AaronChuzb/TD3/hardwave/SD卡内容（将里边的文件复制到SD卡根目录下）/jpg/2.jpg

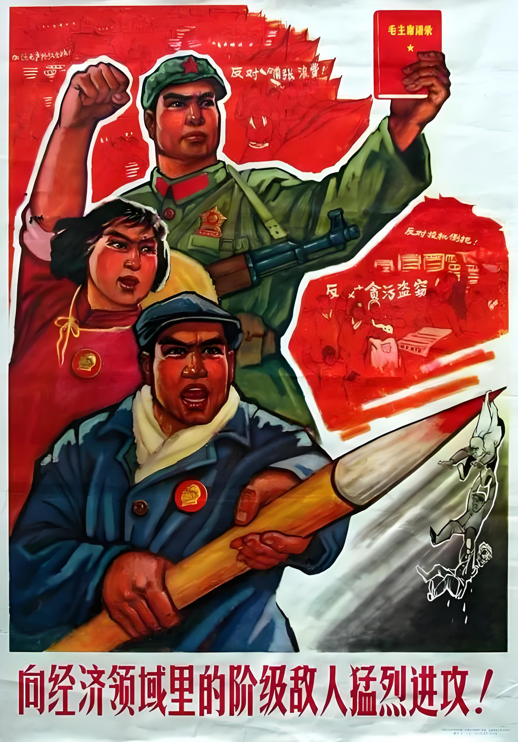
hardwave/SD卡内容（将里边的文件复制到SD卡根目录下）/jpg/2.jpg
