AaronChuzb/TD3/hardwave/SD卡内容（将里边的文件复制到SD卡根目录下）/png/1.png

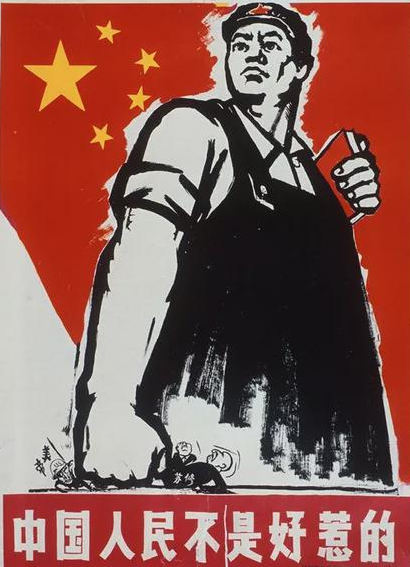
hardwave/SD卡内容（将里边的文件复制到SD卡根目录下）/png/1.png
