AaronChuzb/TD3/main/HAL/HAL_wifi.c

/*
 * @Date: 2024-03-23 22:36:39
 * @LastEditors: AaronChu
 * @LastEditTime: 2024-07-23 16:47:45
 */
#include "HAL.h"

/* FreeRTOS event group to signal when we are connected*/
static EventGroupHandle_t s_wifi_event_group;

static const char *TAG = "WIFI";

static int s_retry_num = 0;

static void event_handler(void *arg, esp_event_base_t event_base,
                          int32_t event_id, void *event_data)
{
  if (event_base == WIFI_EVENT && event_id == WIFI_EVENT_STA_START)
  {
    esp_wifi_connect();
  }
  else if (event_base == WIFI_EVENT && event_id == WIFI_EVENT_STA_DISCONNECTED)
  {
    if (s_retry_num < 5)
    {
      esp_wifi_connect();
      s_retry_num++;
      ESP_LOGI(TAG, "retry to connect to the AP");
    }
    else
    {
      xEventGroupSetBits(s_wifi_event_group, WIFI_FAIL_BIT);
    }
    ESP_LOGI(TAG, "connect to the AP fail");
  }
  else if (event_base == IP_EVENT && event_id == IP_EVENT_STA_GOT_IP)
  {
    ip_event_got_ip_t *event = (ip_event_got_ip_t *)event_data;
    ESP_LOGI(TAG, "got ip:" IPSTR, IP2STR(&event->ip_info.ip));
    s_retry_num = 0;
    xEventGroupSetBits(s_wifi_event_group, WIFI_CONNECTED_BIT);
  }
}

void wifi_init_sta(void)
{
  s_wifi_event_group = xEventGroupCreate();

  ESP_ERROR_CHECK(esp_netif_init());

  ESP_ERROR_CHECK(esp_event_loop_create_default());
  esp_netif_create_default_wifi_sta();

  wifi_init_config_t cfg = WIFI_INIT_CONFIG_DEFAULT();
  ESP_ERROR_CHECK(esp_wifi_init(&cfg));

  esp_event_handler_instance_t instance_any_id;
  esp_event_handler_instance_t instance_got_ip;
  ESP_ERROR_CHECK(esp_event_handler_instance_register(WIFI_EVENT,
                                                      ESP_EVENT_ANY_ID,
                                                      &event_handler,
                                                      NULL,
                                                      &instance_any_id));
  ESP_ERROR_CHECK(esp_event_handler_instance_register(IP_EVENT,
                                                      IP_EVENT_STA_GOT_IP,
                                                      &event_handler,
                                                      NULL,
                                                      &instance_got_ip));

  wifi_config_t wifi_config = {
      .sta = {
          .ssid = WIFI_SSID,
          .password = WIFI_PASS,
          .threshold.authmode = WIFI_AUTH_WPA_WPA2_PSK,
      },
  };
  // ESP_ERROR_CHECK(esp_wifi_set_storage(WIFI_STORAGE_FLASH));
  ESP_ERROR_CHECK(esp_wifi_set_mode(WIFI_MODE_STA));
  ESP_ERROR_CHECK(esp_wifi_set_config(WIFI_IF_STA, &wifi_config));
  ESP_ERROR_CHECK(esp_wifi_start());
  // 降低发射功率
  esp_wifi_set_max_tx_power(16);

  ESP_LOGI(TAG, "wifi_init_sta finished.");

  /* Waiting until either the connection is established (WIFI_CONNECTED_BIT) or connection failed for the maximum
   * number of re-tries (WIFI_FAIL_BIT). The bits are set by event_handler() (see above) */
  EventBits_t bits = xEventGroupWaitBits(s_wifi_event_group,
                                         WIFI_CONNECTED_BIT | WIFI_FAIL_BIT,
                                         pdFALSE,
                                         pdFALSE,
                                         portMAX_DELAY);

  /* xEventGroupWaitBits() returns the bits before the call returned, hence we can test which event actually
   * happened. */
  if (bits & WIFI_CONNECTED_BIT)
  {
    ESP_LOGI(TAG, "connected to ap SSID:%s password:%s",
             WIFI_SSID, WIFI_PASS);
    lv_msg_send(MSG_WIFI_IS_CONNECTED, NULL);
  }
  else if (bits & WIFI_FAIL_BIT)
  {
    ESP_LOGI(TAG, "Failed to connect to SSID:%s, password:%s",
             WIFI_SSID, WIFI_PASS);
    lv_msg_send(MSG_WIFI_NOT_CONNECTED, NULL);
  }
  else
  {
    ESP_LOGE(TAG, "UNEXPECTED EVENT");
  }
}

void wifi_scan_task()
{
  nvs_flash_init();
  wifi_init_config_t cfg = WIFI_INIT_CONFIG_DEFAULT();
  esp_wifi_init(&cfg);
  esp_wifi_set_storage(WIFI_STORAGE_FLASH);
  esp_wifi_set_mode(WIFI_MODE_STA);
  esp_wifi_start();

  wifi_scan_config_t scan_config = {
      .ssid = 0,
      .bssid = 0,
      .channel = 0,
      .show_hidden = true};
  // 通常认为-70dbm以上为理想的信号强度，-70 dbm～-80 dbm为中等信号强度，
  // 小于-80dbm为弱信号，多数企业级AP可以接收到-95dbm左右的信号。
  while (1)
  {
    esp_wifi_scan_start(&scan_config, true);
    uint16_t ap_num = 0;
    esp_wifi_scan_get_ap_num(&ap_num);
    wifi_ap_record_t *ap_list = (wifi_ap_record_t *)malloc(sizeof(wifi_ap_record_t) * ap_num);
    esp_wifi_scan_get_ap_records(&ap_num, ap_list);
    printf("ap_num:%d\n", ap_num);
    if (ap_num == 0)
    {
      printf("扫描失败!\n");
      vTaskDelay(1000 / portTICK_PERIOD_MS);
      continue;
    }

    printf("扫描成功:\n");
    for (int i = 0; i < ap_num; i++)
    {
      printf("WiFi ID: %s\t信号强度: %d\n", (char *)ap_list[i].ssid, ap_list[i].rssi);
    }

    free(ap_list);
    vTaskDelay(10000 / portTICK_PERIOD_MS);
  }

  esp_wifi_stop();
  esp_wifi_deinit();
}

void init_wifi(void)
{
  // wifi_scan_task();
  // Initialize NVS
  esp_err_t ret = nvs_flash_init();
  if (ret == ESP_ERR_NVS_NO_FREE_PAGES || ret == ESP_ERR_NVS_NEW_VERSION_FOUND)
  {
    ESP_ERROR_CHECK(nvs_flash_erase());
    ret = nvs_flash_init();
  }
  ESP_ERROR_CHECK(ret);

  ESP_LOGI(TAG, "ESP_WIFI_MODE_STA");
  wifi_init_sta();
}
