AaronChuzb/TD3/main/HAL/HAL_beep.c

/*
 * @Date: 2024-04-02 21:33:12
 * @LastEditors: AaronChu
 * @LastEditTime: 2024-04-18 19:19:54
 */
#include "HAL.h"

#define P 0
#define L1 1
#define L1_ 2
#define L2 3
#define L2_ 4
#define L3 5
#define L4 6
#define L4_ 7
#define L5 8
#define L5_ 9
#define L6 10
#define L6_ 11
#define L7 12
#define M1 13
#define M1_ 14
#define M2 15
#define M2_ 16
#define M3 17
#define M4 18
#define M4_ 19
#define M5 20
#define M5_ 21
#define M6 22
#define M6_ 23
#define M7 24
#define H1 25
#define H1_ 26
#define H2 27
#define H2_ 28
#define H3 29
#define H4 30
#define H4_ 31
#define H5 32
#define H5_ 33
#define H6 34
#define H6_ 35
#define H7 36

// 索引与频率对照表
unsigned int FreqTable[] = {
    0, // 休止符，表示不弹
    262,
    277,
    294,
    311,
    330,
    349,
    370,
    392,
    415,
    440,
    466,
    496,
    523,
    554,
    587,
    622,
    659,
    698,
    740,
    784,
    831,
    880,
    932,
    988,
    1046,
    1109,
    1175,
    1245,
    1318,
    1397,
    1480,
    1568,
    1661,
    1760,
    1865,
    1976,
};


struct YINFU
{ // 定义音符
  int freq;
  int Duration;
};

struct YINFU MUSIC[512] = {
    {P, 4},
    {P, 4},
    {P, 4},
    {M6, 2},
    {M7, 2},
    {H1, 4 + 2},
    {M7, 2},
    {H1, 4},
    {H3, 4},
    {M7, 4 + 4 + 4},
    {M3, 2},
    {M3, 2},
    {M6, 4 + 2},
    {M5, 2},
    {M6, 4},
    {H1, 4},
    {M5, 4 + 4 + 4},
    {M3, 4},
    {M4, 4 + 2},
    {M3, 2},
    {M4, 4},
    {H1, 4},
    {M3, 4 + 4},
    {P, 2},
    {H1, 2},
    {H1, 2},
    {H1, 2},
    {M7, 4 + 2},
    {M4_, 2},
    {M4_, 4},
    {M7, 4},
    {M7, 8},
    {P, 4},
    {M6, 2},
    {M7, 2},
    {H1, 4 + 2},
    {M7, 2},
    {H1, 4},
    {H3, 4},
    {M7, 4 + 4 + 4},
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

struct YINFU YUEPU[128] = {
    {831, 300},
    {740, 300},
    {622, 300},
    {740, 300},
    {988, 300},
    {831, 150},
    {740, 150},
    {831, 400},
    {0, 300},
    {0, 300},
    {622, 300},
    {740, 300},
    {831, 300},
    {740, 300},
    {622, 300},
    {494, 150},
    {440, 150},
    {740, 150},
    {622, 150},
    {554, 400},
    {0, 300},
    {554, 300},
    {622, 300},
    {740, 300},
    {740, 300},
    {831, 300},
    {622, 150},
    {554, 150},
    {494, 400},
    {0, 300},
    {0, 300},
    {740, 300},
    {622, 300},
    {554, 150},
    {494, 150},
    {440, 150},
    {494, 150},
    {392, 500},
    {0, 300},
    {0, 300},
};


void midi_task(void *arg)
{
  int index = 0;
  int flag = 0;
  while (1)
  {
    setBeepTone(FreqTable[MUSIC[index].freq]);
    vTaskDelay((MUSIC[index].Duration * 125) / portTICK_PERIOD_MS);
    index += 1;
    if (index > 119)
    {
      flag += 1;
      index = 0;
    }
    if (flag == 2)
    {
      ledc_set_duty(LEDC_LOW_SPEED_MODE, LEDC_CHANNEL_1, 0);
      ledc_update_duty(LEDC_LOW_SPEED_MODE, LEDC_CHANNEL_1);
      vTaskSuspend(NULL);
    }
  }
}

void init_tone()
{
  xTaskCreateWithCaps(midi_task, "midi", 1024 * 30, NULL, 3, NULL, MALLOC_CAP_SPIRAM);
}
