AaronChuzb/TD3/components/lsm6ds3/include/lsm6ds3.h

/*
 * @Date: 2024-01-31 16:12:11
 * @LastEditors: AaronChu
 * @LastEditTime: 2024-06-17 16:37:08
 */
#pragma once

#ifndef LSM6DS3_H
#define LSM6DS3_H

#ifdef __cplusplus
extern "C"
{
#endif

#include <stdio.h>
#include "i2c.h"

#define LSM_REG_ID 0x6A

typedef struct
{
  float ax;
  float ay;
  float az;
  float gx;
  float gy;
  float gz;
  float mx;
  float my;
  float mz;
  float temp;
  float roll;
  float pitch;
  float yaw;
} gyro_data_t;

  // esp_err_t bmp280_restart();
  // esp_err_t bmp280_read_param();
  // esp_err_t bmp280_measure_cmd();
  // esp_err_t bmp280_read_data();
  esp_err_t lsm6ds3_get_id();
  esp_err_t lsm6ds3_get_gyroscope();
  esp_err_t lsm6ds3_get_accelerometer();
  
  void init_lsm6ds3();
  gyro_data_t lsm6ds3_get_all_data();

#ifdef __cplusplus
} /*extern "C"*/
#endif

#endif
