AaronChuzb/TD3/components/pcf8563/include/pcf8563.h

/*
 * @Date: 2024-01-31 16:12:11
 * @LastEditors: AaronChu
 * @LastEditTime: 2024-06-04 10:05:54
 */
#pragma once

#ifndef PCF8563_H
#define PCF8563_H

#ifdef __cplusplus
extern "C"
{
#endif

#include <stdio.h>
#include "esp_log.h"
#include "esp_system.h"
#include "i2c.h"
#include <time.h>
// #include <sys/time.h>

#define PCF_REG_ID 0x51

bool initialized_pcf8563();
void init_pcf8563();
esp_err_t pcf8563_set_time(struct tm *time);
esp_err_t pcf8563_get_time(struct tm *time);
// void setBackLightLevel(int level);
  

#ifdef __cplusplus
} /*extern "C"*/
#endif

#endif
